mehdilauters/esp8266-rfid/user/rfid.c

#include "rfid.h"
#include "main.h"
#include "config.h"
#include <string.h>
#include "espressif/esp_common.h"
#include <esp/uart.h>

#include "lwip/sockets.h"
#include "lwip/err.h"
#include "lwip/sys.h"
#include <netdb.h>

#include "tags.h"

#define TAG_START 0x02
#define TAG_STOP 0x03

#define HTTPS_REQUEST "GET /tag.json?serial=%d&tagid=%s HTTP/1.0\r\nHost: %s\r\n\r\n"

tag_t m_tag;

bool m_reading = false;
int button_pressed = 0;
bool button_processed = false;

static int m_port;
static char m_server[256];


void tag_init(tag_t * _tag)
{
  memset(_tag->id, 0, TAG_ID_LENGTH);
  _tag->current_index = 0;
  _tag->valid = false;
}

bool tag_feed(tag_t *_tag, uint8_t _val) {
  if(_tag->current_index < TAG_ID_LENGTH) {
    printf("=%x=",_val);
//     printf("ID\n");
    _tag->id[_tag->current_index] = _val;
  } else if(_tag->current_index > TAG_ID_LENGTH && _tag->current_index <= TAG_ID_LENGTH + TAG_CHECKSUM_LENGTH) {

  } else {
    // cr // lf
  }
  _tag->current_index++;
  return true;
}

void push_tag(char *_tag) {
  tag_init(&m_tag);
  int i;
  for(i=0; i < strlen(_tag); i++)
  {
    tag_feed(&m_tag, _tag[i]);
  }
  m_tag.valid = true;
  set_green_led(true);
}

bool send_tag() {
  int sockfd;
  struct sockaddr_in serverSockAddr;
  struct hostent *serverHostEnt;
  long hostAddr;
  bzero(&serverSockAddr,sizeof(serverSockAddr));
  hostAddr = inet_addr(m_server);
  if ( (long)hostAddr != (long)-1)
    bcopy(&hostAddr,&serverSockAddr.sin_addr,sizeof(hostAddr));
  else
  {
    serverHostEnt = gethostbyname(m_server);
    if (serverHostEnt == NULL)
    {
      printf("gethost fail\n");
      return false;
    }
    bcopy(serverHostEnt->h_addr,&serverSockAddr.sin_addr,serverHostEnt->h_length);
  }
  serverSockAddr.sin_port = htons(m_port);
  serverSockAddr.sin_family = AF_INET;
  
  if ( (sockfd = socket(AF_INET,SOCK_STREAM,0)) < 0) {
    printf("failed to create socket");
    return false;
  }
  
  if(connect( sockfd,
    (struct sockaddr *)&serverSockAddr,
              sizeof(serverSockAddr)) < 0 ) {
    printf("conection failed");
  return false;
  }
  
#ifdef RAW_TCP
  write(sockfd, m_tag.id, TAG_ID_LENGTH);
  printf("raw send\n");
#else
  char buf[TAG_ID_LENGTH +1];
  memset(buf, 0, TAG_ID_LENGTH+1);
  for(int i=0; i < TAG_ID_LENGTH; i++) {
    buf[i] = m_tag.id[i];
  }
  buf[TAG_ID_LENGTH] = '\0';
  char buffer[strlen(HTTPS_REQUEST) + 128];
  uint32_t id = sdk_system_get_chip_id();
  int res = sprintf(buffer, HTTPS_REQUEST, id, buf, m_server);
  if(write(sockfd, buffer, res) < 0) {
    printf("http write fail\n");
    }
  printf("%s\n",buffer);
  printf(buffer);
  static char recv_buf[128];
  int r;
  do {
    bzero(recv_buf, 128);
    r = read(sockfd, recv_buf, 127);
    if(r > 0) {
      printf("%s", recv_buf);
    }
  } while(r > 0);
#endif
  shutdown(sockfd,2);
  close(sockfd);
  set_green_led(false);
  return true;
}

void tag_process() {
  printf("Processing tag\n");
  if(is_connected()) {
    send_tag();
  } else {
   printf("not connected\n"); 
  }
}

// static void button_triggered() {
//   tag_init(&m_tag);
//   int i;
//   for(i=0; i < strlen(BUTTON_TAG_VALUE); i++)
//   {
//     tag_feed(&m_tag, BUTTON_TAG_VALUE[i]);
//   }
//   m_tag.valid = true;
// }
// 
// static void process_button() {
//   if(get_button_pressed() ) {
//     if(button_pressed > BUTTON_PRESSED_DELAY && ! button_processed)
//     {
//       button_processed = true;
//       button_triggered();
//     }
//     button_pressed ++;
//   } else {
//     button_processed = false;
//     button_pressed = 0;
//   }
// }

static void feed_task(void *pvParameters)
{
  while(true) {
    
    vTaskDelay(1);
    uint8_t c;
    if(get_serial(&c)) {
      if(c == TAG_START) {
        m_reading = true;
        tag_init(&m_tag);
      } else {
        if(c == TAG_STOP) {
          m_reading = false;
          m_tag.valid = true;
          set_green_led(true);
        }
        if(m_reading) {
          tag_feed(&m_tag, c);
        }
      }
    }    
  }
}


static void rfid_task(void *pvParameters)
{
  while(true) {
    if(m_tag.valid) {
      m_tag.valid = false;
      tag_process();
    }
    vTaskDelay(10);
  }
}

void rfid_start() {
  printf("RFID start\n");
  
  m_tag.valid = false;
  m_tag.current_index = 0;
  
  memset(m_server, 0, 256);
  m_port = 0;
  load_server(m_server, &m_port);
  
  xTaskCreate(feed_task, (const char *)"feed_task", 512, NULL, 3, NULL);
  xTaskCreate(rfid_task, (const char *)"rfid_task", 512, NULL, 3, NULL);
}
